juliorrsantos/SignalMixer/LTspice/Simulacao_do_circuito.asc

C1: cap; 100n
C2: cap; 100n
R1: res; 10K
R2: res; 10K
R3: res; 50R
R4: res; 10K
R5: res; 10K
R6: res; 10K
R7: res; 10K
R8: res; 10K
R9: res; 10K
R10: res; 10K
R11: res; 10K
R12: res; 10K
R13: res; 10K
R14: res; 10Meg
U1: UniversalOpAmp
U2: UniversalOpAmp
U3: UniversalOpAmp
U4: UniversalOpAmp
V1: voltage; 24
V2: voltage; SINE(0 1 60)
V3: voltage; SINE(0 1 1200)
Named nets: +24Vcc, 0, GNDS
.tran 660m
Amplificadores com Ganho = 1
